tomcircuit/MAX7000S-CPLD-JTAG-Tester/media/IMG_4214.jpg

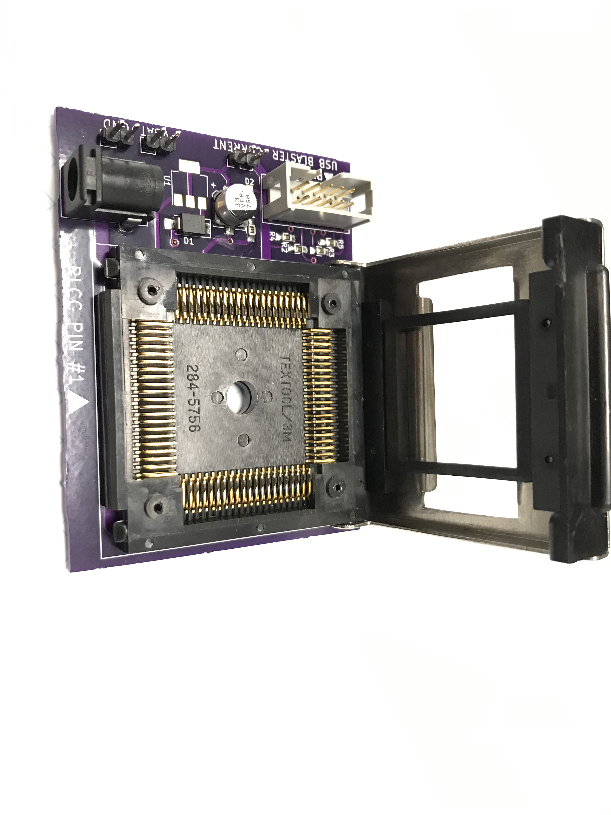
media/IMG_4214.jpg
